TheSlowGrowth/MonomeArcClone/firmware/PotBoard/i2c_s.h

/*	 This file contains source code for the firmware of a monome arc 
 *   clone.
 * 
 *   Copyright (C) 2013  Johannes Neumann; mail@johannesneumann.net
 *
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
 *   You should have received a copy of the GNU General Public License
 *   along with this program.  If not, see <http://www.gnu.org/licenses/>.
 */  
 

#ifndef I2C_MAX_MESSAGE_OUT_LENGTH
	#error I2C_MAX_MESSAGE_OUT_LENGTH is not defined
#endif
#ifndef I2C_MAX_MESSAGE_IN_LENGTH
	#error I2C_MAX_MESSAGE_IN_LENGTH is not defined
#endif

#ifndef I2C_BUFFER_OUT_LENGTH
	#error I2C_BUFFER_OUT_LENGTH is not defined
#endif
#ifndef I2C_BUFFER_IN_LENGTH
	#error I2C_BUFFER_IN_LENGTH is not defined
#endif

struct i2c_message_out 
{
	uint8_t length;
	uint8_t data[I2C_MAX_MESSAGE_OUT_LENGTH];
};

struct i2c_message_in 
{
	uint8_t length;
	uint8_t error;
	uint8_t data[I2C_MAX_MESSAGE_IN_LENGTH];
};


// inits the interface
void i2c_init(uint8_t adress);
// returns the adress, this slave is working with
uint8_t i2c_getAdress( void );

// appends a message to be sent
int8_t i2c_hasOutgoingMessages( void );
int8_t i2c_hasIncomingMessages( void );

int8_t i2c_canTakeNewOutgoingMessage( void );
int8_t i2c_canTakeNewIncomingMessage( void );

volatile struct i2c_message_in* i2c_getInputBufferBack( void );
volatile struct i2c_message_in* i2c_getInputBufferFront( void );
void i2c_removeInputBufferBack( void );
int8_t i2c_addInputBufferFront( volatile struct i2c_message_in m );

volatile struct i2c_message_out* i2c_getOutputBufferBack( void );
volatile struct i2c_message_out* i2c_getOutputBufferFront( void );
void i2c_removeOutputBufferBack( void );
int8_t i2c_addOutputBufferFront( volatile struct i2c_message_out m );

void i2c_trySendMessages( void );


// internal definitions

#define I2C_clock 300000L

// Status codes for i2c Slave Receiver Mode (TWSR)
#define I2C_SLA_W_received_ack_returned 0x60
#define I2C_SLA_W_received_upon_arbitration_lost 0x68
#define I2C_GCALL_received_ack_returned 0x70
#define I2C_GCALL_received_upon_arbitration_lost 0x78
#define I2C_SLA_W_data_received_ack_returned 0x80
#define I2C_SLA_W_data_received_nack_returned 0x88
#define I2C_GCALL_data_received_ack_returned 0x90
#define I2C_GCALL_data_received_nack_returned 0x98
#define I2C_stop_or_start_while_adressed 0xA0

// Status codes for i2c Slave Transmitter Mode
#define I2C_SLA_R_received_ack_returned 0xA8
#define I2C_data_sent_ack_received 0xB8
#define I2C_data_sent_nack_received 0xC0
#define I2C_last_data_sent_ack_received 0xC8

#define I2C_IN_ERROR_OVERFLOW 0b00000001

#define I2C_ENABLE  (1<<TWEN) | (1<<TWINT) | (1<<TWIE)
#define I2C_ACK     (1<<TWEA) | I2C_ENABLE
#define I2C_NACK    I2C_ENABLE
#define I2C_START   (1<<TWSTA) | I2C_ENABLE
#define I2C_STOP    (1<<TWSTO) | I2C_ENABLE
